drzwave/ZRAD/Test/RangeTesting/202408ShawFields.csv

Time | Latitude | Longitude | Altitude | TxPower | RSSI | Mon Aug 12 2024 15:44:09 GMT-0400 (Eastern Daylight Time)
03:44:09 PM | 43.166072845458984 | -70.86975860595703 | -9.39 | 8 | -49
03:44:09 PM | 43.16604995727539 | -70.8697738647461 | 1.33 | -6 | -61
03:44:09 PM | 43.166015625 | -70.86978149414062 | 16.66 | -6 | -73
03:44:09 PM | 43.166019439697266 | -70.86976623535156 | 20.9 | -6 | -60
03:44:09 PM | 43.166019439697266 | -70.8697509765625 | 23.05 | -6 | -66
03:44:09 PM | 43.1660270690918 | -70.86974334716797 | 23.96 | -6 | -65
03:44:09 PM | 43.16603088378906 | -70.86974334716797 | 24.14 | -6 | -60
03:44:09 PM | 43.166046142578125 | -70.86974334716797 | 23.49 | -6 | -62
03:44:09 PM | 43.16604232788086 | -70.8697509765625 | 24.24 | -6 | -51
03:44:09 PM | 43.166046142578125 | -70.86975860595703 | 26.07 | -6 | -63
03:44:09 PM | 43.166080474853516 | -70.86973571777344 | 25.63 | -6 | -72
03:44:09 PM | 43.16610336303711 | -70.86968994140625 | 25.98 | -6 | -79
03:44:09 PM | 43.16616439819336 | -70.86956024169922 | 25.44 | -6 | -78
03:44:09 PM | 43.16625213623047 | -70.86941528320312 | 25.75 | -6 | -79
03:44:09 PM | 43.16624069213867 | -70.86927032470703 | 28.73 | -6 | -99
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
